Makerspace-Amiens-2025-26/Puzzle-Bot-Groupe03/docs/images/Capture d'écran 2026-06-13 232701.png

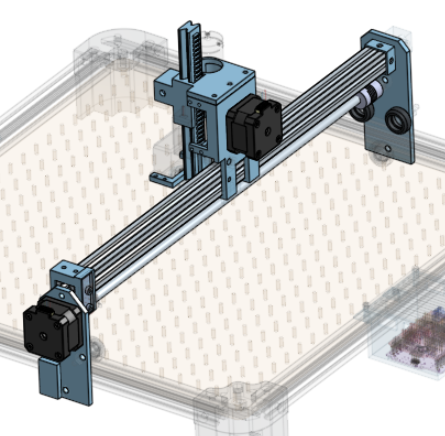
docs/images/Capture d'écran 2026-06-13 232701.png
