Makerspace-Amiens-2025-26/Puzzle-Bot-Groupe03/docs/images/Cerveau.jpeg

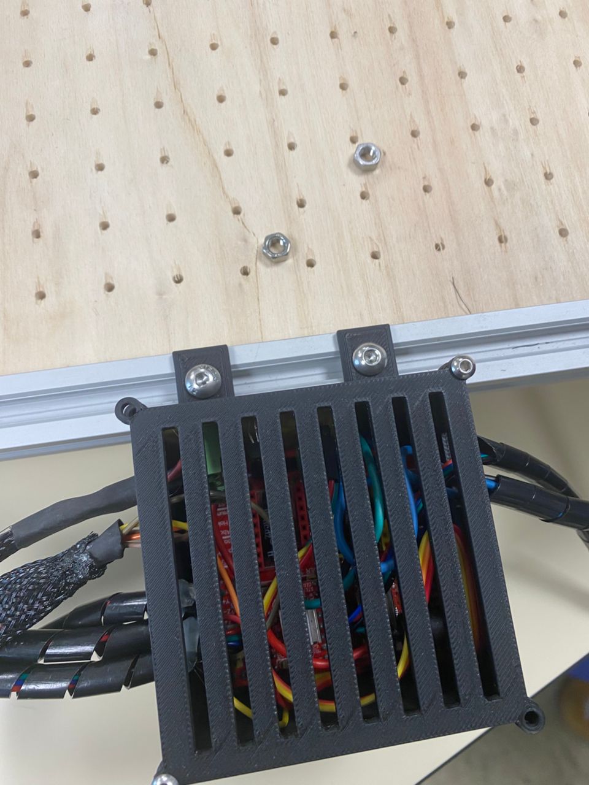
docs/images/Cerveau.jpeg
