Makerspace-Amiens-2025-26/Puzzle-Bot-Groupe03/docs/images/groupe 3.jpeg

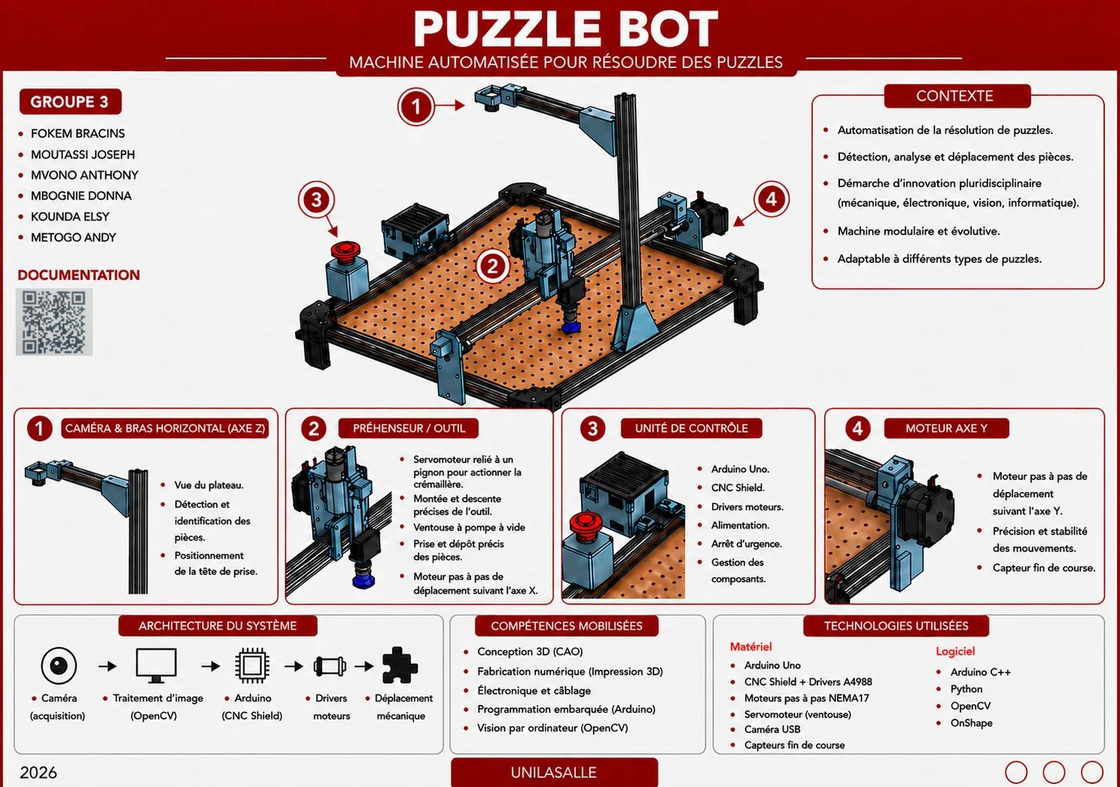
docs/images/groupe 3.jpeg
