Makerspace-Amiens-2025-26/Puzzle-Bot-Groupe03/docs/images/WhatsApp Image 2026-06-1.jpeg

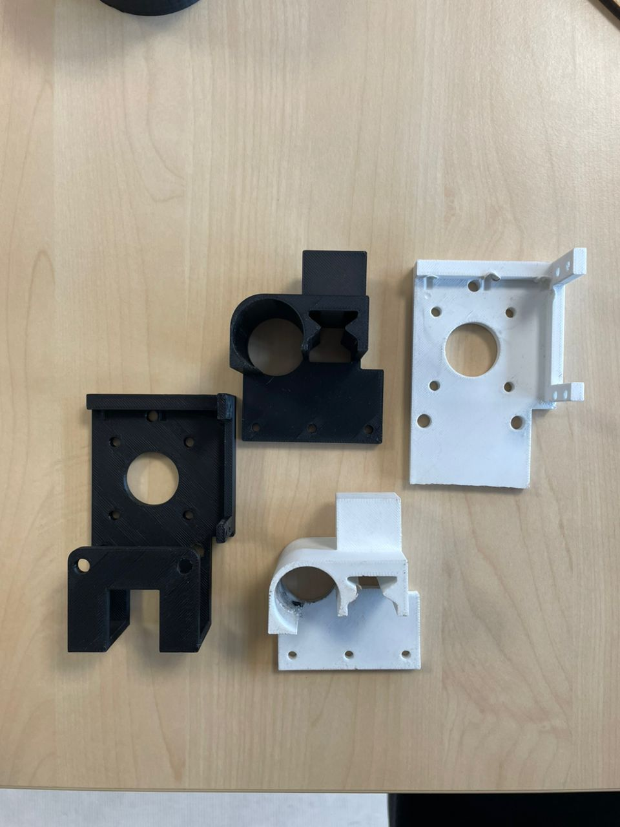
docs/images/WhatsApp Image 2026-06-1.jpeg
