Makerspace-Amiens-2025-26/Puzzle-Bot-Groupe03/docs/images/WhatsApp Image 2026-06-13 at 13.234.jpeg

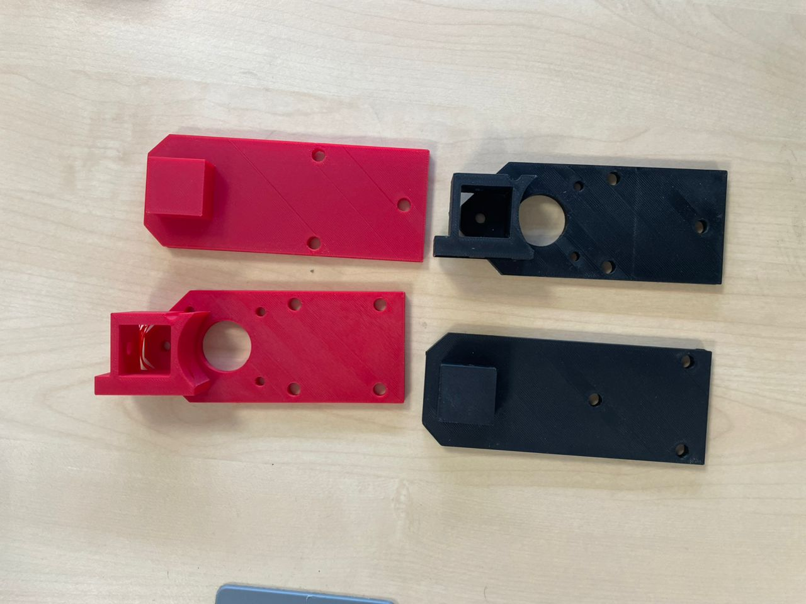
docs/images/WhatsApp Image 2026-06-13 at 13.234.jpeg
